hcarver/8_bit_computer_schematics/alu_v2_bb.png

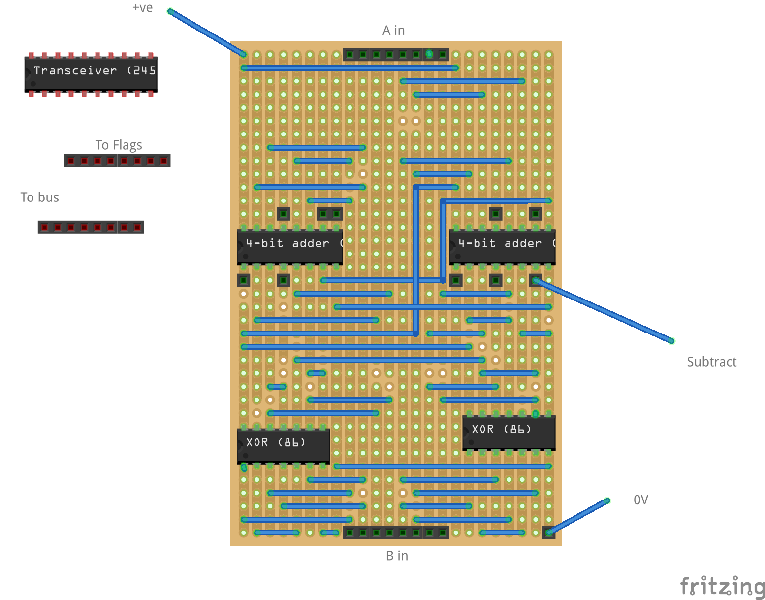
alu_v2_bb.png
