hcarver/8_bit_computer_schematics/clock_bb.png

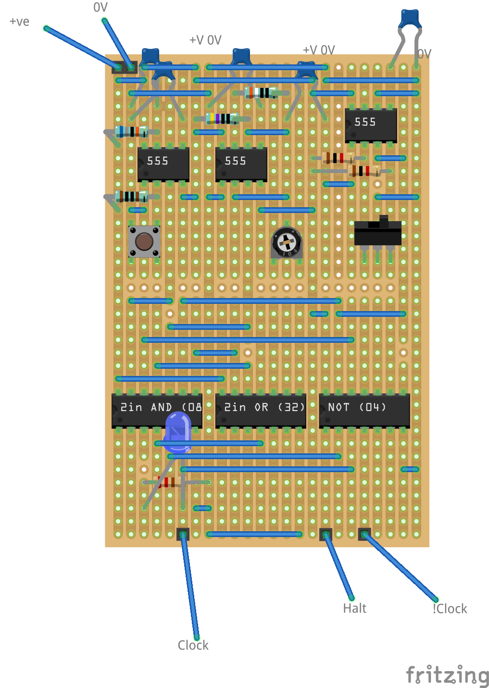
clock_bb.png
