hcarver/8_bit_computer_schematics/ir_bb.png

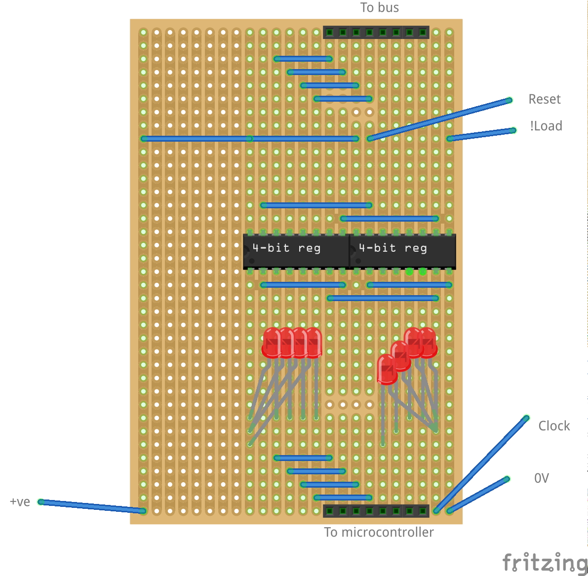
ir_bb.png
