hcarver/8_bit_computer_schematics/pc_bb.png

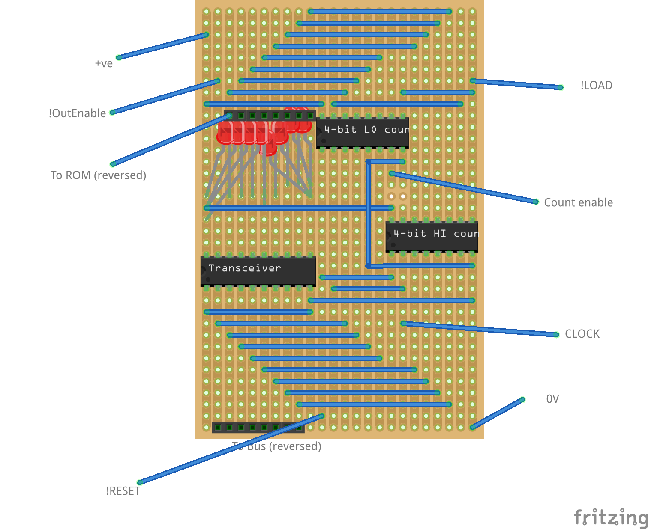
pc_bb.png
