hcarver/8_bit_computer_schematics/ram_bb.png

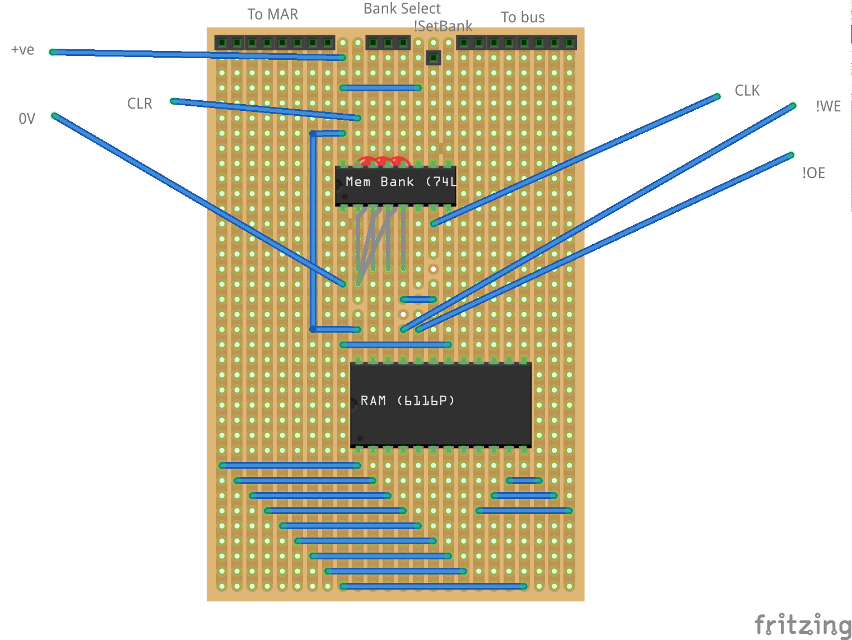
ram_bb.png
