hcarver/8_bit_computer_schematics/alu_flags_bb_no_parts.png

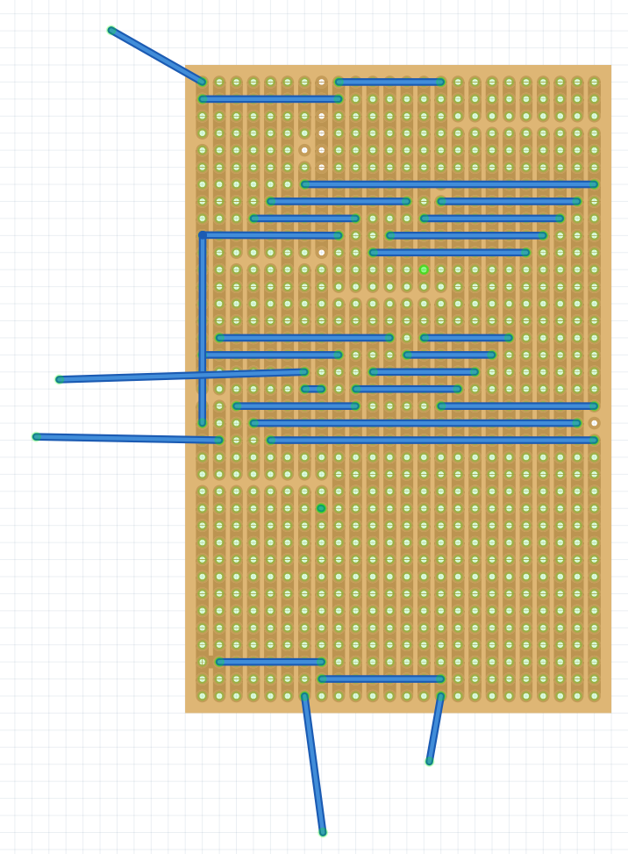
alu_flags_bb_no_parts.png
