hcarver/8_bit_computer_schematics/alu_v2_bb_no_parts.png

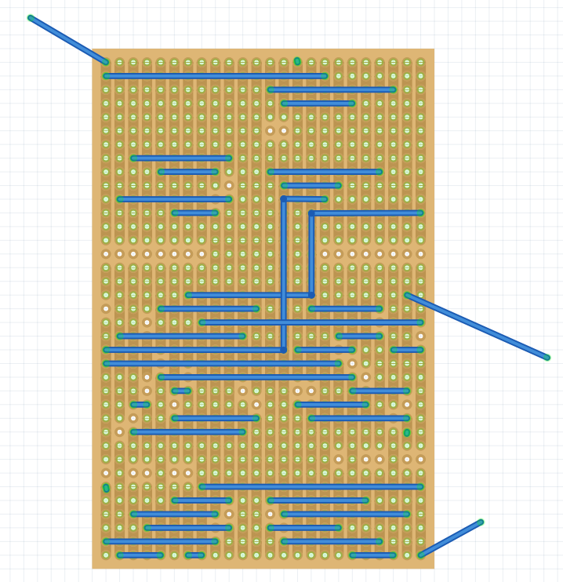
alu_v2_bb_no_parts.png
