hcarver/8_bit_computer_schematics/eeprom_programmer_v2_bb_no_parts.png

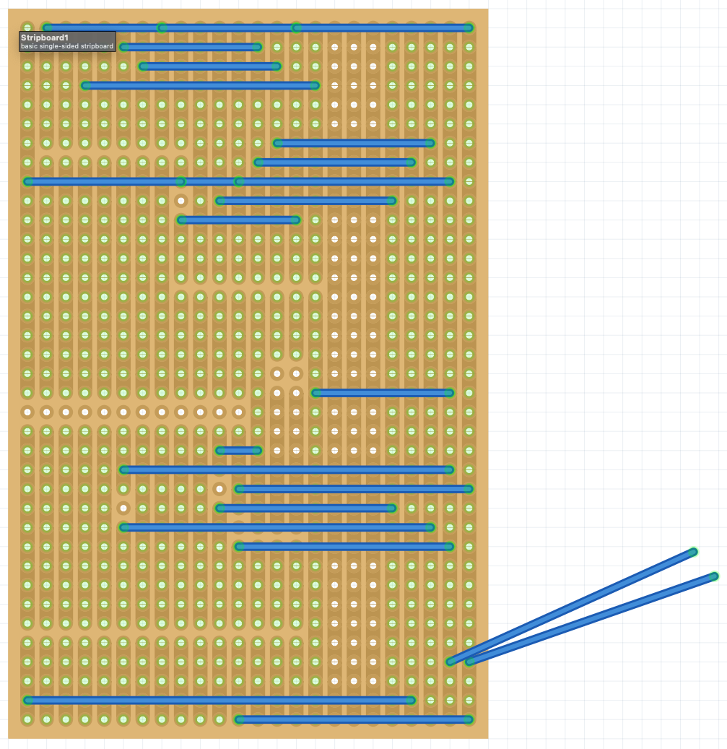
eeprom_programmer_v2_bb_no_parts.png
