hcarver/8_bit_computer_schematics/ir_bb_no_parts.png

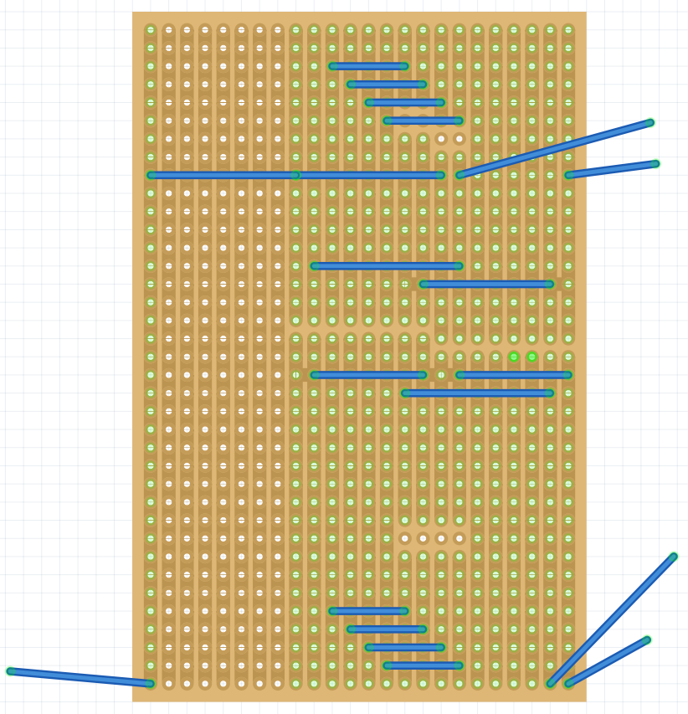
ir_bb_no_parts.png
