hcarver/8_bit_computer_schematics/mar_bb_no_parts.png

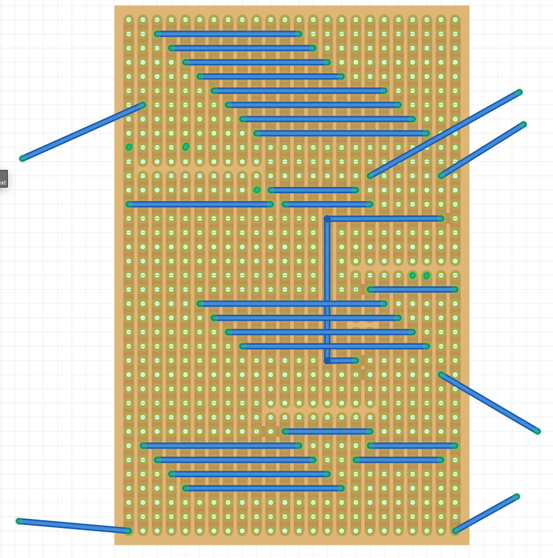
mar_bb_no_parts.png
