hcarver/8_bit_computer_schematics/ram_bb_no_parts.png

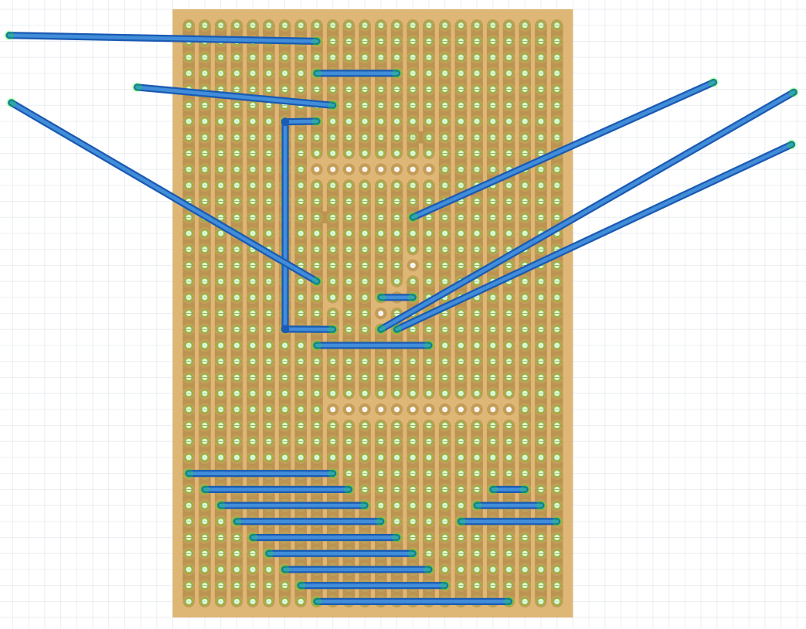
ram_bb_no_parts.png
