hcarver/8_bit_computer_schematics/register_bb_no_parts.png

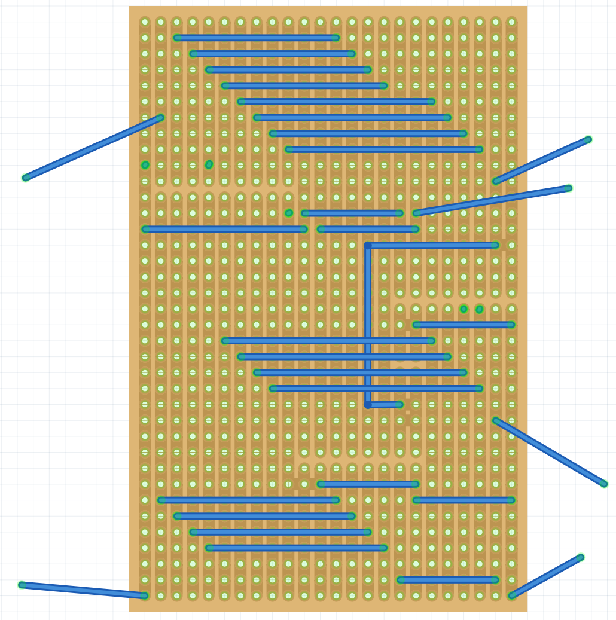
register_bb_no_parts.png
