hcarver/8_bit_computer_schematics/rom_bb_no_parts.png

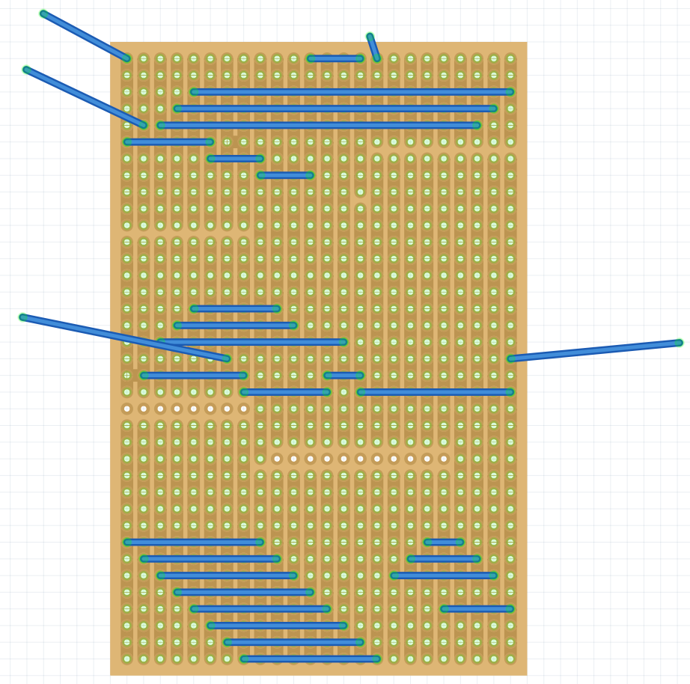
rom_bb_no_parts.png
